yeounhyeok/openclaw-IoT-system/sketch/arduino_secrets.example.h

// Copy this file to arduino_secrets.h before uploading to the board.
// Keep arduino_secrets.h private because it contains WiFi and Home Assistant tokens.

#define SECRET_WIFI_SSID "YOUR_WIFI_SSID"
#define SECRET_WIFI_PASSWORD "YOUR_WIFI_PASSWORD"

#define SECRET_HA_HOST "ha.yeoun.org"
#define SECRET_HA_PORT 443
#define SECRET_HA_TOKEN "YOUR_HOME_ASSISTANT_LONG_LIVED_ACCESS_TOKEN"
